outadoc/bttf-speedometer-arduino/pictures/IMG_1453.jpg

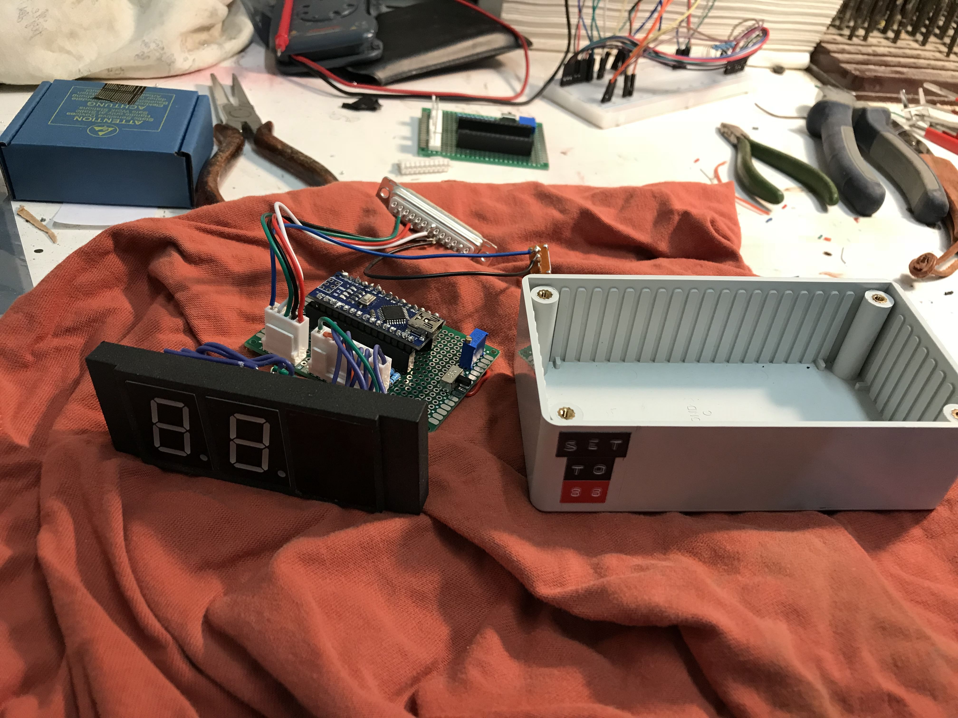
pictures/IMG_1453.jpg
