outadoc/bttf-speedometer-arduino/pictures/IMG_1499.jpg

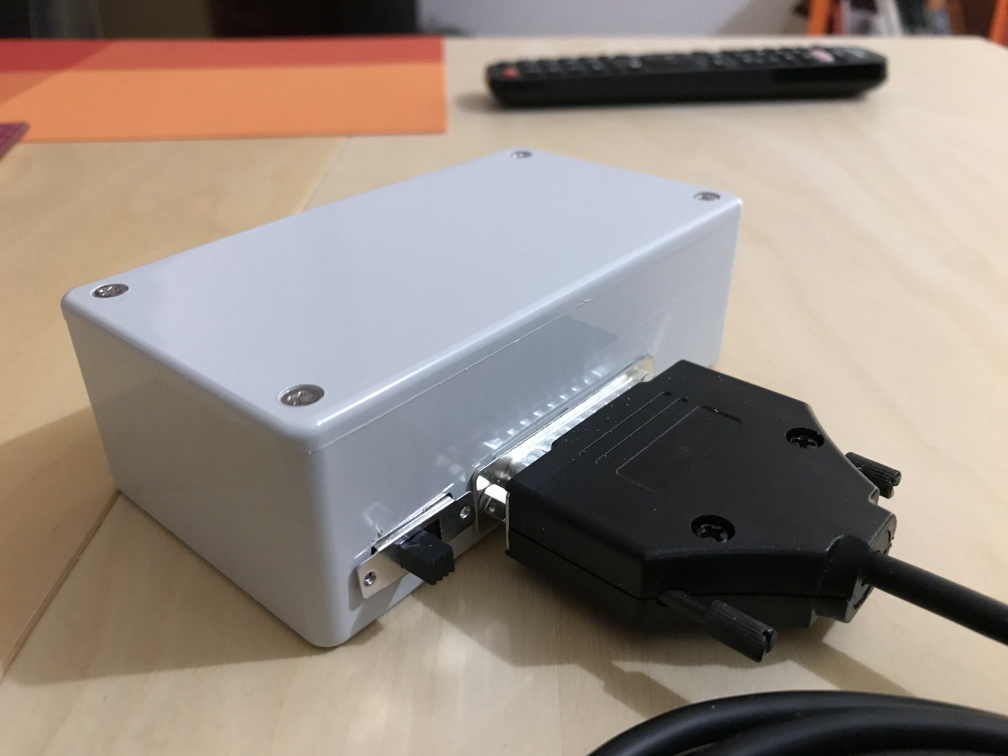
pictures/IMG_1499.jpg
