outadoc/bttf-speedometer-arduino/pictures/IMG_1510.jpg

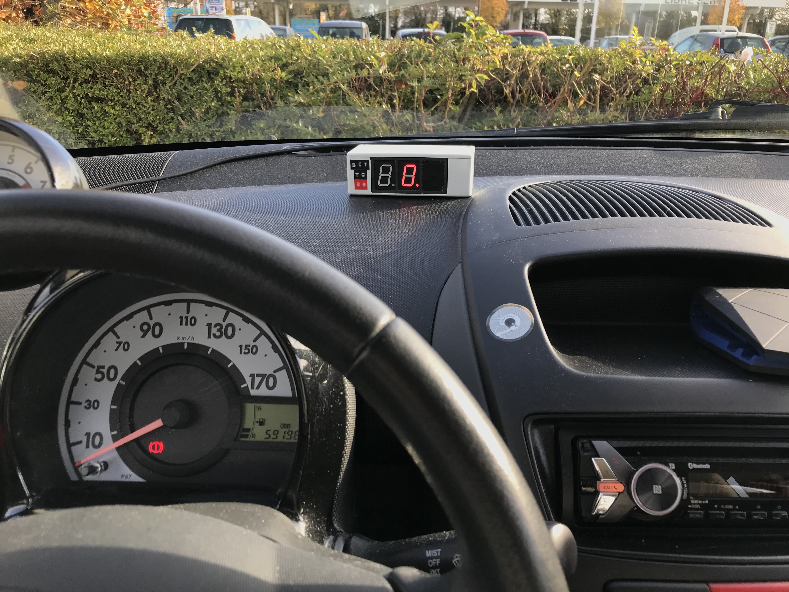
pictures/IMG_1510.jpg
