outadoc/bttf-speedometer-arduino/pictures/IMG_20170826_182334.jpg

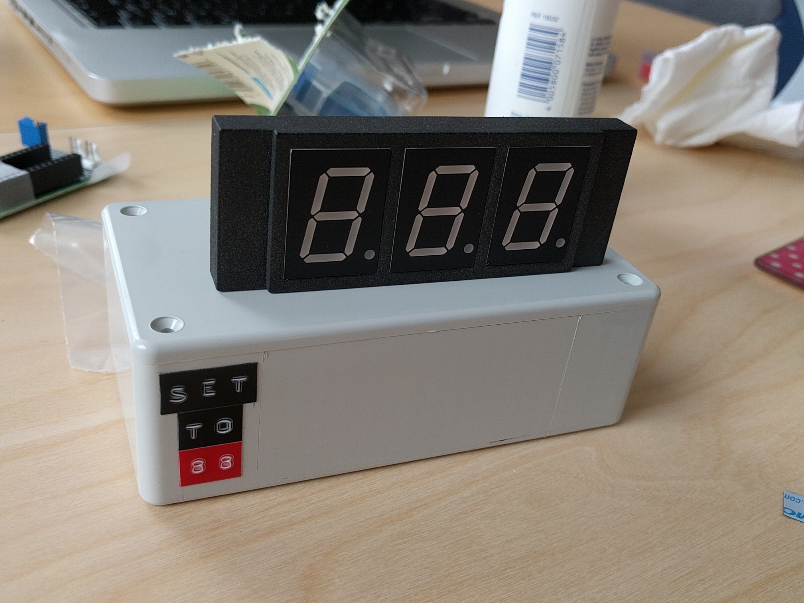
pictures/IMG_20170826_182334.jpg
