outadoc/bttf-speedometer-arduino/references/bttf1_screen_87_front.png

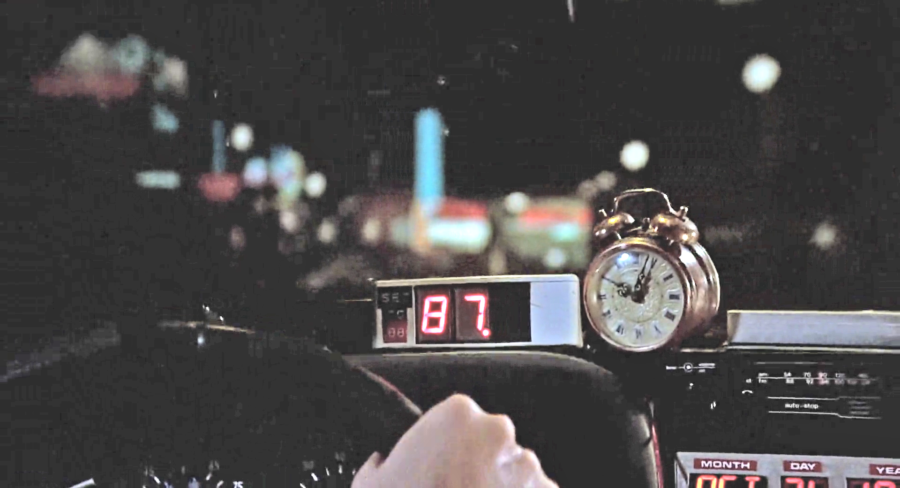
references/bttf1_screen_87_front.png
