outadoc/bttf-speedometer-arduino/references/de_meulemester_speedo_1.jpg

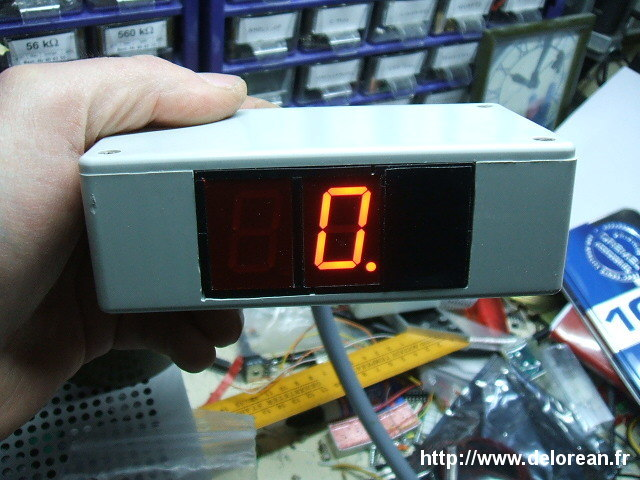
references/de_meulemester_speedo_1.jpg
