outadoc/bttf-speedometer-arduino/references/de_meulemester_speedo_2.jpg

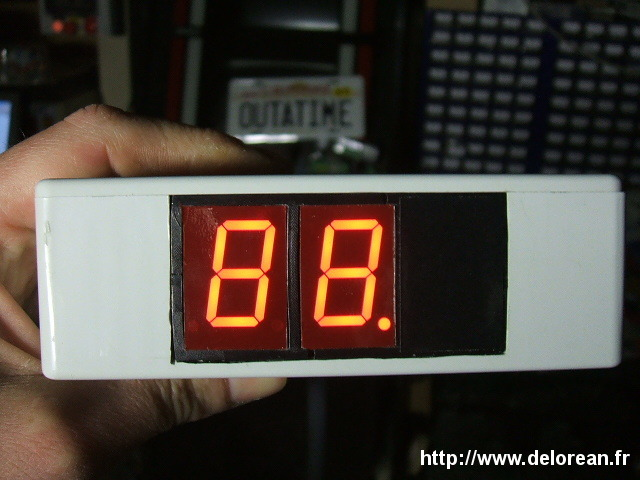
references/de_meulemester_speedo_2.jpg
